brighamtaft/practicum/breadboard_proto.jpg

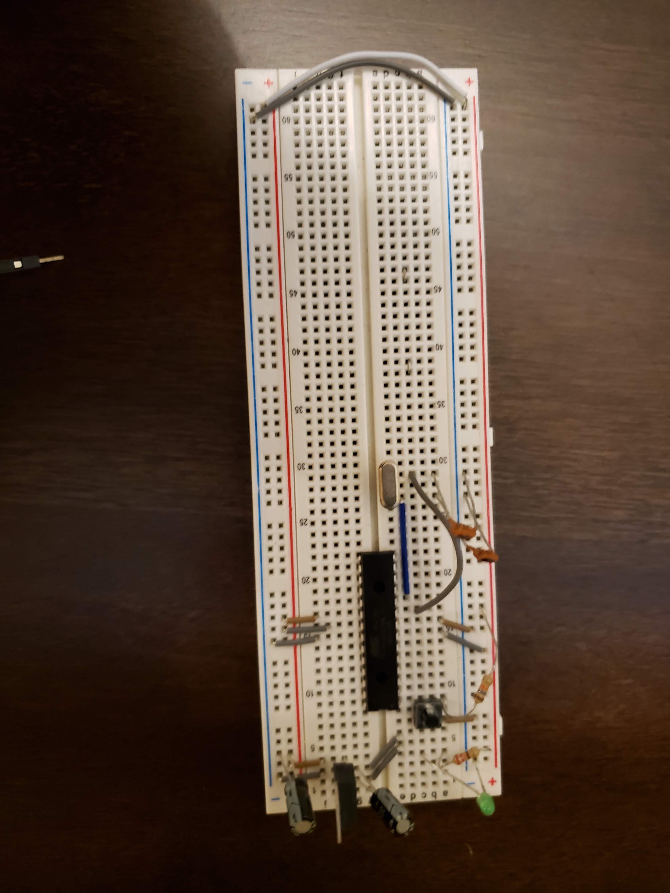
breadboard_proto.jpg
